elkayem/Mandelbrot-Explorer/VHDL/colormap_roygold.vhd

library ieee;
use ieee.std_logic_1164.all;
use ieee.numeric_std.all;
entity colormap_roygold is
   port(
      clk: in std_logic;
      addr: in std_logic_vector(7 downto 0);
      data: out std_logic_vector(11 downto 0)
   );
end colormap_roygold;

architecture arch of colormap_roygold is
   constant ADDR_WIDTH: integer:=8;
   constant DATA_WIDTH: integer:=12;
   type rom_type is array (0 to 2**ADDR_WIDTH-1)
        of std_logic_vector(DATA_WIDTH-1 downto 0);
   -- ROM definition
   constant colormap: rom_type:=(  -- 2^4-by-12
     x"000",
      x"b69",
      x"b69",
      x"b69",
      x"b59",
      x"b59",
      x"b59",
      x"b59",
      x"b59",
      x"b58",
      x"b58",
      x"b58",
      x"b58",
      x"b48",
      x"a48",
      x"a48",
      x"a48",
      x"a48",
      x"a47",
      x"a47",
      x"a47",
      x"a37",
      x"a37",
      x"a37",
      x"a37",
      x"a37",
      x"a37",
      x"a36",
      x"a36",
      x"a36",
      x"a26",
      x"a26",
      x"a26",
      x"a26",
      x"a26",
      x"a26",
      x"a25",
      x"925",
      x"915",
      x"915",
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
      x"5ab",
      x"5ac",
      x"4bc",
      x"4bc",
      x"4cd",
      x"4cd",
      x"3de",
      x"3de",
      x"3ee",
      x"3ef",
      x"2ff",
      x"2ff",
      x"2ff",
      x"2ff",
      x"2ee",
      x"2ee",
      x"2ee",
      x"2ed",
      x"2dd",
      x"2dd",
      x"2dc",
      x"2dc",
      x"2cc",
      x"2cb",
      x"2cb",
      x"2cb",
      x"2ca",
      x"2ba",
      x"2ba",
      x"1b9",
      x"1b9",
      x"1a9",
      x"1a8",
      x"1a8",
      x"1a8",
      x"197",
      x"197",
      x"197",
      x"196",
      x"186",
      x"186",
      x"185",
      x"185",
      x"185",
      x"174",
      x"174",
      x"174",
      x"173",
      x"163",
      x"163",
      x"162",
      x"162",
      x"152",
      x"151",
      x"151",
      x"151",
      x"151",
      x"151",
      x"151",
      x"152",
      x"142",
      x"142",
      x"242",
      x"242",
      x"242",
      x"242",
      x"242",
      x"243",
      x"243",
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
   );
   signal addr_reg: std_logic_vector(ADDR_WIDTH-1 downto 0);
begin
   -- addr register to infer block RAM
   process (clk)
   begin
      if (clk'event and clk = '1') then
        addr_reg <= addr;
      end if;
   end process;
   data <= colormap(to_integer(unsigned(addr_reg)));
end arch;
