elkayem/Mandelbrot-Explorer/VHDL/colormap_wild.vhd

library ieee;
use ieee.std_logic_1164.all;
use ieee.numeric_std.all;
entity colormap_wild is
   port(
      clk: in std_logic;
      addr: in std_logic_vector(7 downto 0);
      data: out std_logic_vector(11 downto 0)
   );
end colormap_wild;

architecture arch of colormap_wild is
   constant ADDR_WIDTH: integer:=8;
   constant DATA_WIDTH: integer:=12;
   type rom_type is array (0 to 2**ADDR_WIDTH-1)
        of std_logic_vector(DATA_WIDTH-1 downto 0);
   -- ROM definition
   constant colormap: rom_type:=(  -- 2^4-by-12
      x"333",
      x"ed3",
      x"ed3",
      x"ed3",
      x"ed3",
      x"ed3",
      x"ed3",
      x"ed3",
      x"ed3",
      x"ed2",
      x"ed2",
      x"ed2",
      x"ed2",
      x"c57",
      x"ed3",
      x"ed3",
      x"ed3",
      x"ed3",
      x"ed3",
      x"ed3",
      x"ec3",
      x"ec3",
      x"ec3",
      x"ec3",
      x"ec3",
      x"ec3",
      x"ec3",
      x"ec3",
      x"ec3",
      x"ec3",
      x"ec3",
      x"ec3",
      x"eb3",
      x"eb3",
      x"eb4",
      x"eb4",
      x"eb4",
      x"eb4",
      x"eb4",
      x"eb4",
      x"eb4",
      x"eb4",
      x"db4",
      x"db4",
      x"da4",
      x"da4",
      x"da4",
      x"da4",
      x"da4",
      x"da4",
      x"da4",
      x"da4",
      x"da4",
      x"da4",
      x"da5",
      x"da5",
      x"da5",
      x"d95",
      x"d95",
      x"d95",
      x"d95",
      x"d95",
      x"d95",
      x"d95",
      x"d95",
      x"d95",
      x"d95",
      x"d95",
      x"d95",
      x"d85",
      x"d85",
      x"d85",
      x"d85",
      x"d85",
      x"d86",
      x"d86",
      x"d86",
      x"d86",
      x"d86",
      x"d86",
      x"d86",
      x"c86",
      x"c76",
      x"c76",
      x"c76",
      x"c76",
      x"c76",
      x"c76",
      x"c76",
      x"c76",
      x"c76",
      x"c76",
      x"c76",
      x"c76",
      x"c67",
      x"c67",
      x"c67",
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
   );
   signal addr_reg: std_logic_vector(ADDR_WIDTH-1 downto 0);
begin
   -- addr register to infer block RAM
   process (clk)
   begin
      if (clk'event and clk = '1') then
        addr_reg <= addr;
      end if;
   end process;
   data <= colormap(to_integer(unsigned(addr_reg)));
end arch;
